sidlauskaslukas/barbot/client/src/assets/images/cocktails/cape_codder.png

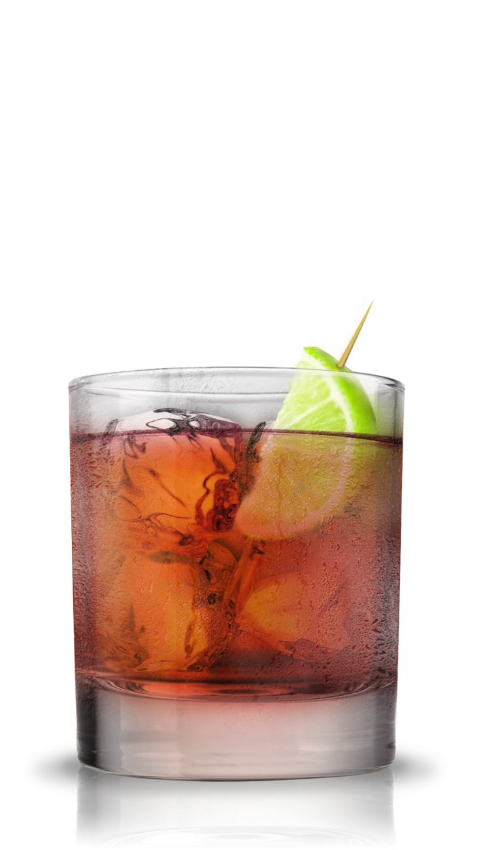
client/src/assets/images/cocktails/cape_codder.png
