sidlauskaslukas/barbot/client/src/assets/images/cocktails/cuba_libre.png

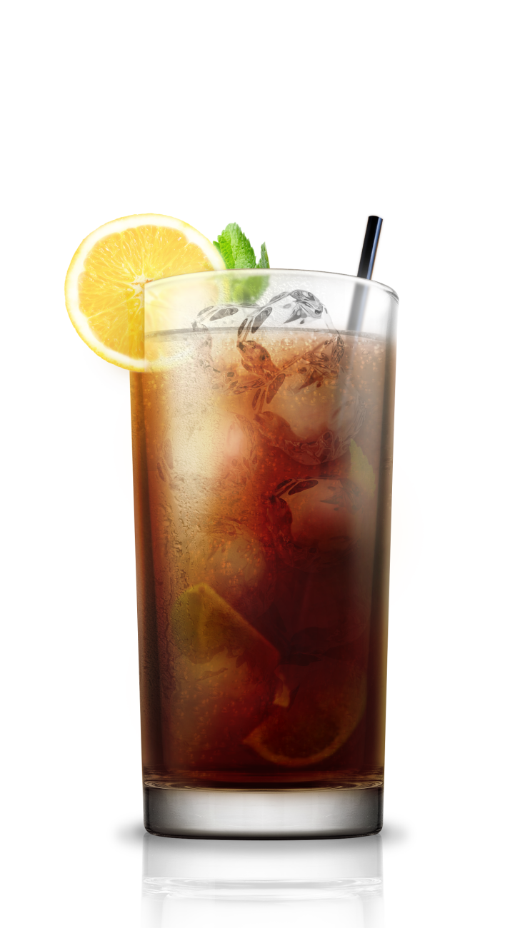
client/src/assets/images/cocktails/cuba_libre.png
