sidlauskaslukas/barbot/client/src/assets/images/cocktails/feeling_lucky_small.png

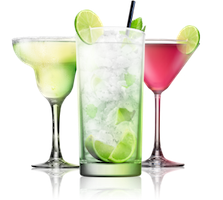
client/src/assets/images/cocktails/feeling_lucky_small.png
