sidlauskaslukas/barbot/client/src/assets/images/cocktails/fuzzy_navel.png

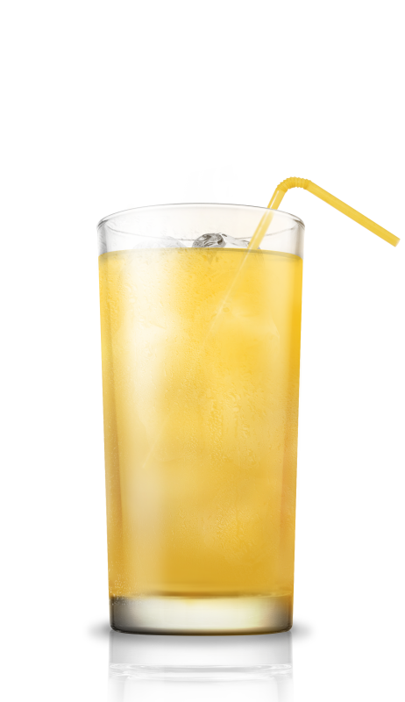
client/src/assets/images/cocktails/fuzzy_navel.png
