sidlauskaslukas/barbot/client/src/assets/images/cocktails/melon_ball.png

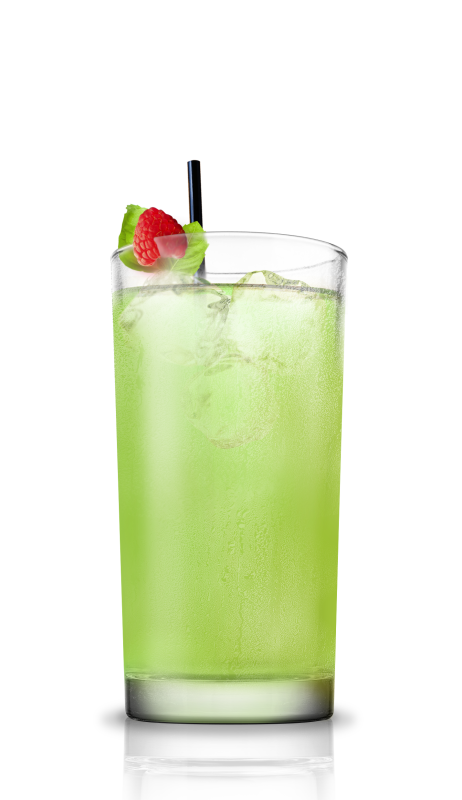
client/src/assets/images/cocktails/melon_ball.png
