sidlauskaslukas/barbot/client/src/assets/images/cocktails/screw_driver.png

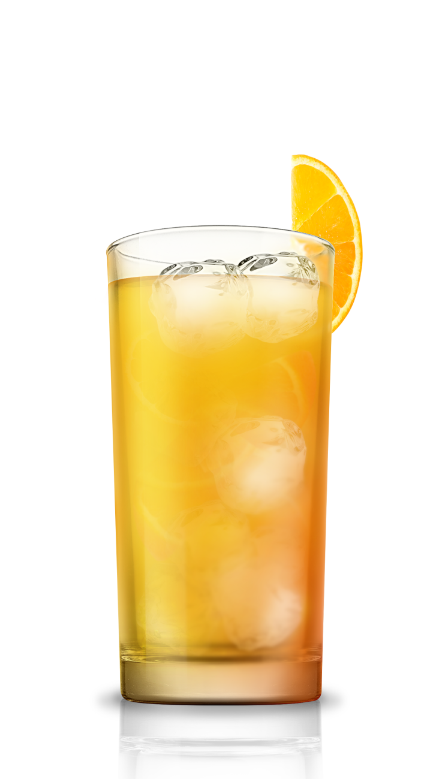
client/src/assets/images/cocktails/screw_driver.png
