sidlauskaslukas/barbot/client/src/assets/images/cocktails/sex_on_the_beach.png

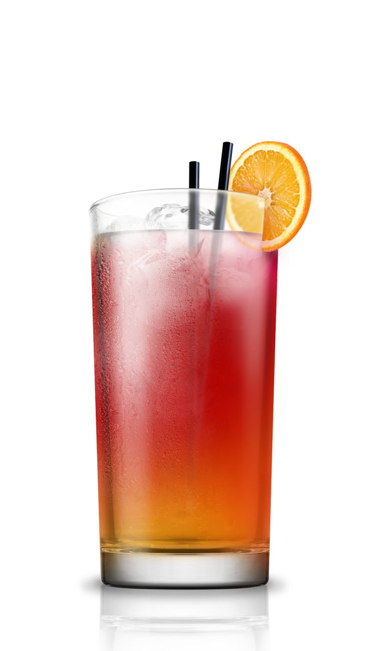
client/src/assets/images/cocktails/sex_on_the_beach.png
