sidlauskaslukas/barbot/client/src/assets/images/cocktails/wild_wild_west.png

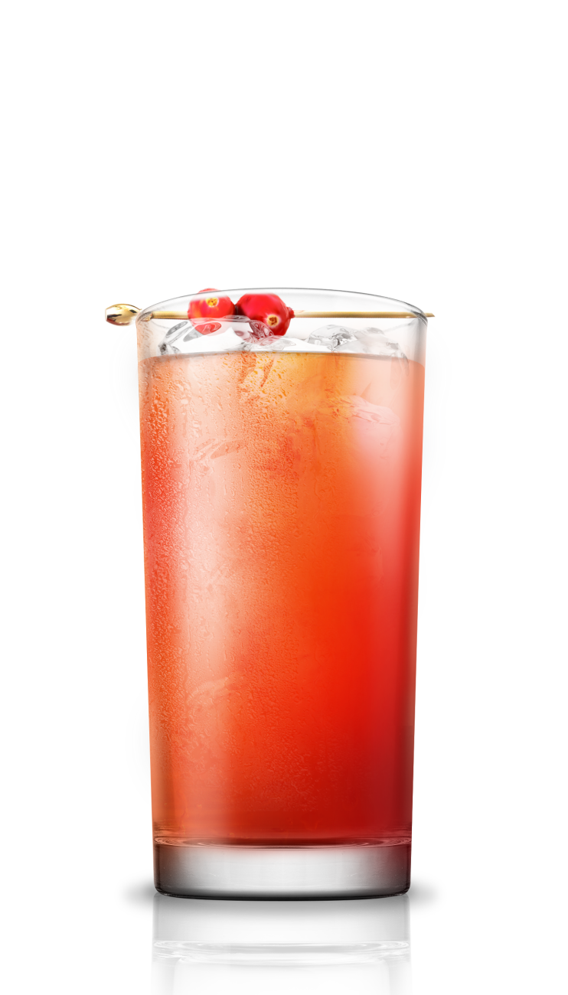
client/src/assets/images/cocktails/wild_wild_west.png
