sidlauskaslukas/barbot/client/src/assets/images/cocktails/woo_woo.png

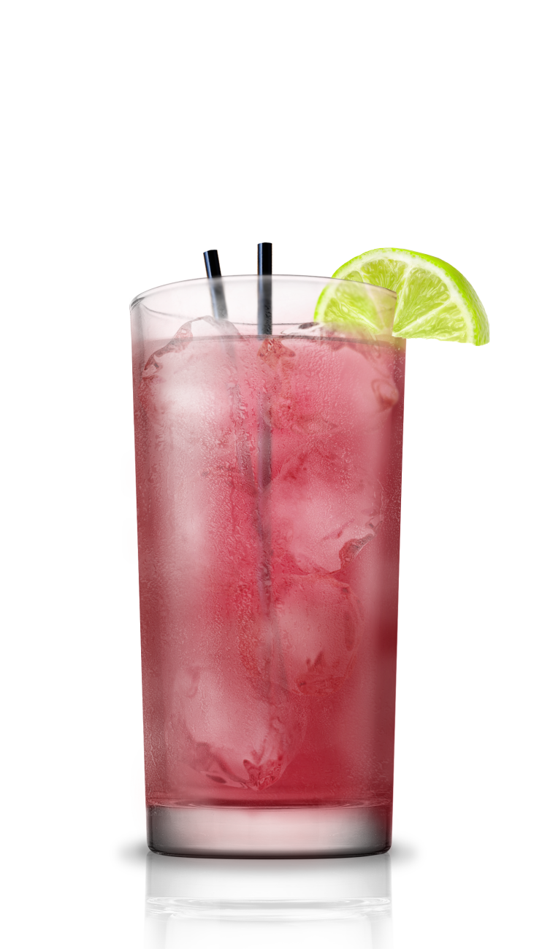
client/src/assets/images/cocktails/woo_woo.png
